opiopan/simhid-g1000/firmware/src/command.c

/*
 * command.c
 *  Author: Hiroshi Murayama <opiopan@gmail.com>
 */

#include <stdio.h>
#include <string.h>
#include <ctype.h>
#include "project.h"
#include "appmain.h"
#include "option.h"
#include "version.h"
#include "command.h"
#include "olog.h"

static const char* PRODUCTNAME = "SimHID G1000";
static const char* MANUFACTURER = "Hiroshi Murayama <opiopan@gmail.com>";
static const char* PROTOCOL = "SimHID protocol V1";

/*========================================================
 Error message
========================================================*/
static const char *ERR_SYNTAX = "syntax error";
static const char* ERR_TOOLONG = "too long line";
static const char* ERR_TOOMANYPARAM = "parameters of command must be less than 10";
static const char* ERR_NOCMD = "not supported command";
static const char* ERR_NOOPT = "unknown option name";
static const char *ERR_INVBOOLOPT = "option value must be 0 or 1";
static const char *ERR_INVINTOPT = "option value must be integer";
static const char *ERR_TOOLONGOPT = "too long option value";

/*========================================================
 Command parser implementation
========================================================*/
void command_parser_init(CommandParserCtx * ctx, char *buf, int len)
{
    ctx->phase = PARSE_INIT;
    ctx->linebuf = buf;
    ctx->linebuflen = len;
    ctx->parsedlen = 0;
    ctx->paramnum = 0;
    ctx->command = -1;
    ctx->err = NULL;
}

static inline BOOL isSeparator(int c)
{
    return c == ' ' || c == '\t';
}

static inline BOOL isCommand(int c)
{
    return (c >= 'A' && c <= 'Z') || (c >= 'a' && c <= 'z');
}

static inline BOOL isNumeric(int c)
{
    return c >= '0' && c <= '9';
}

BOOL command_parser_parse(CommandParserCtx *ctx, int c)
{
    BOOL rc = FALSE;

    if (ctx->phase == PARSE_END){
        ctx->phase = PARSE_INIT;
        ctx->parsedlen = 0;
        ctx->paramnum = 0;
        ctx->command = -1;
        ctx->err = NULL;
    }

    if (ctx->parsedlen == ctx->linebuflen && ctx->phase != PARSE_SKIP){
        ctx->phase = PARSE_SKIP;
        ctx->err = ERR_TOOLONG;
    }
    if (ctx->phase != PARSE_SKIP || ctx->phase != PARSE_EOL){
        ctx->linebuf[ctx->parsedlen++] = c;
    }

    switch (ctx->phase){
    case PARSE_INIT:{
        if (isSeparator(c)){
            /* nothing to do */
        }else if (isCommand(c)){
            ctx->phase = PARSE_POSTCOMMAND;
            ctx->command = c;
        }else if (c == '\r'){
            ctx->phase = PARSE_EOL;
        }else{
            ctx->phase = PARSE_SKIP;
            ctx->err = ERR_SYNTAX;
        }
        break;
    }
    case PARSE_POSTCOMMAND:{
        if (isSeparator(c)){
            ctx->phase = PARSE_SEPARATOR;
        }else if (c == '\r'){
            ctx->phase = PARSE_EOL;
        }else{
            ctx->phase = PARSE_SKIP;
            ctx->err = ERR_SYNTAX;
        }
        break;
    }
    case PARSE_SEPARATOR:{
        if (isSeparator(c)){
            /* nothing to do */
        }else if (c == '\r'){
            ctx->phase = PARSE_EOL;
        }else if (ctx->paramnum >= COMMAND_MAX_PARAM){
            ctx->phase = PARSE_SKIP;
            ctx->err = ERR_TOOMANYPARAM;
        }else{
            CommandParam* param = ctx->params + ctx->paramnum++;
            param->strvalue = ctx->linebuf + ctx->parsedlen - 1;
            param->isNumber = FALSE;
            param->len = 1;
            if (c == '-'){
                ctx->phase = PARSE_MINUSNUMBER;
            }else if (isNumeric(c)){
                ctx->phase = PARSE_NUMBER;
                param->numvalue = c - '0';
            }else{
                ctx->phase = PARSE_STRING;
            }
        }
        break;
    }
    case PARSE_MINUSNUMBER:{
        if (isSeparator(c)){
            ctx->phase = PARSE_SEPARATOR;
        }else if (c == '\r'){
            ctx->phase = PARSE_EOL;
        }else{
            CommandParam *param = ctx->params + ctx->paramnum - 1;
            param->len++;
            if (isNumeric(c)){
                ctx->phase = PARSE_NUMBER;
                param->numvalue = -(c - '0');
            }else{
                ctx->phase = PARSE_STRING;
            }
        }
        break;
    }
    case PARSE_NUMBER:{
        CommandParam *param = ctx->params + ctx->paramnum - 1;
        if (isSeparator(c)){
            ctx->phase = PARSE_SEPARATOR;
            param->isNumber = TRUE;
            ctx->linebuf[ctx->parsedlen - 1] = '\0';
        }else if (c == '\r'){
            ctx->phase = PARSE_EOL;
            param->isNumber = TRUE;
            ctx->linebuf[ctx->parsedlen - 1] = '\0';
        }else{
            param->len++;
            if (isNumeric(c)){
                param->numvalue *= 10;
                param->numvalue += param->numvalue > 0 ? 
                                   c - '0' : -(c - '0');
            }else{
                ctx->phase = PARSE_STRING;
            }
        }
        break;
    }
    case PARSE_STRING:{
        CommandParam *param = ctx->params + ctx->paramnum - 1;
        if (isSeparator(c)){
            ctx->phase = PARSE_SEPARATOR;
            ctx->linebuf[ctx->parsedlen - 1] = '\0';
        }else if (c == '\r'){
            ctx->linebuf[ctx->parsedlen - 1] = '\0';
            ctx->phase = PARSE_EOL;
        }else{
            param->len++;
        }
        break;
    }
    case PARSE_SKIP:{
        if (c == '\r'){
            ctx->phase = PARSE_EOL;
        }
        break;
    }
    case PARSE_EOL:{
        if (c == '\n'){
            ctx->phase = PARSE_END;
            rc = TRUE;
        }else{
            ctx->phase = PARSE_SKIP;
            ctx->err = ERR_SYNTAX;
        }
        break;
    }
    case PARSE_END:{
        /* no condition reach here */
        break;
    }
    }

    return rc;
}

/*========================================================
 Individual command implementation
========================================================*/

/*--------------------------------------------------------
 NOP command
--------------------------------------------------------*/
static void nop_init(void *ctx, CommandParserCtx *cmd)
{
}

static int nop_schedule(void *ctx, char *respbuf, int len)
{
    return 0;
}

static BOOL nop_isfinished(void *ctx)
{
    return TRUE;
}

static CMDOPS cmd_nop = {
    .init = nop_init,
    .schedule = nop_schedule,
    .isfinished = nop_isfinished,
};

/*--------------------------------------------------------
 Error response command
--------------------------------------------------------*/
typedef struct{
    const char* msg;
}ERRCTX;

static void err_init(void *ctx, CommandParserCtx *cmd)
{
    ERRCTX* rctx = (ERRCTX*)ctx;
    rctx->msg = cmd->err;
}

static int err_schedule(void *ctx, char *respbuf, int len)
{
    ERRCTX *rctx = (ERRCTX *)ctx;
    return snprintf(respbuf, len, "E %s\r\n", rctx->msg);
}

static BOOL err_isfinished(void *ctx)
{
    return TRUE;
}

static CMDOPS cmd_err = {
    .init = err_init,
    .schedule = err_schedule,
    .isfinished = err_isfinished,
};

/*--------------------------------------------------------
 Identifier command
--------------------------------------------------------*/
typedef struct{
    int line;
    int maxline;
    int swg_num;
}IDCTX;

static void id_init(void *ctx, CommandParserCtx *cmd)
{
    IDCTX* rctx = (IDCTX*)ctx;
    SCANNER_CTX *scanner = app_getScannerCtx();
    rctx->swg_num = scanner_getswgnum(scanner);
    if (cmd->paramnum > 0 && (strcmp(cmd->params[0].strvalue, "b") == 0 || strcmp(cmd->params[0].strvalue, "B") == 0)){
        rctx->line = 4;
        rctx->maxline = 6 + rctx->swg_num;
    }else{
        rctx->line = 0;
#ifdef ENABLE_RICH_IDENTIFIER
        rctx->maxline == 6 + rctx->swg_num;
#else
        rctx->maxline = 4;
#endif
    }
}

static int id_schedule(void *ctx, char *respbuf, int len)
{
    IDCTX *rctx = (IDCTX *)ctx;
    rctx->line++;
    if (rctx->line == 1){
        return snprintf(respbuf, len, "I Product Name: %s\r\n", PRODUCTNAME);
    }else if (rctx->line == 2){
        return snprintf(respbuf, len, "I Manufacturer: %s\r\n", MANUFACTURER);
    }else if (rctx->line == 3){
        return snprintf(respbuf, len, "I Firmware Version: %s\r\n", version_string);
    }else if (rctx->line == 4){
        return snprintf(respbuf, len, "I Protocol: %s\r\n", PROTOCOL);
    }else if (rctx->line == 5){
        return snprintf(respbuf, len, "I BIT Result:");
    }else if (rctx->line < 6 + rctx->swg_num){
        SCANNER_CTX *scanner = app_getScannerCtx();
        VSWG_CTX* swg =  scanner_getswg(scanner, rctx->line - 6);
        const char* status = swg->is_valid ? "OK" : "Failure";
        return snprintf(respbuf, len, " [%s = %s]", swg->name, status);
    }else if (rctx->line == 6 + rctx->swg_num){
        return snprintf(respbuf, len, "\r\n");
    }

    return 0;
}

static BOOL id_isfinished(void *ctx)
{
    IDCTX *rctx = (IDCTX *)ctx;
    return rctx->line >= rctx->maxline;
}

static CMDOPS cmd_id = {
    .init = id_init,
    .schedule = id_schedule,
    .isfinished = id_isfinished,
};

/*--------------------------------------------------------
 Retrieving switch definitions command
--------------------------------------------------------*/
typedef struct {
    int swgix;
    int swix;
    BOOL completed;
}SWDEFCTX;

static void swdef_init(void *ctx, CommandParserCtx *cmd)
{
    SWDEFCTX* rctx = (SWDEFCTX*)ctx;
    *rctx = (SWDEFCTX){};
}

static int swdef_schedule(void *ctx, char *respbuf, int len)
{
    SWDEFCTX* rctx = (SWDEFCTX*)ctx;
    if (rctx->swgix < 0){
        rctx->completed = TRUE;
        return strlcpy(respbuf, "D\r\n", len);
    }

    SCANNER_CTX *scanner = app_getScannerCtx();
    VSWG_CTX* swg = scanner_getswg(scanner, rctx->swgix);
    VSWITCH_CTX* sw = SWG_GET_SWITCH(swg, rctx->swix);

    int rc = snprintf(respbuf, len, "D %s ", sw->name);
    rc += sw->ops->printdef(sw, respbuf + rc, len - rc);
    rc += strlcpy(respbuf + rc, "\r\n", len - rc);

    rctx->swix++;
    if (rctx->swix >= SWG_GET_SWITCHNUM(swg)){
        rctx->swgix++;
        rctx->swix = 0;
        if (rctx->swgix > scanner_getswgnum(scanner)){
            rctx->swgix = -1;
            rctx->swix = -1;
        }
    }

    return rc;
}

static BOOL swdef_isfinished(void *ctx)
{
    SWDEFCTX *rctx = (SWDEFCTX *)ctx;
    return rctx->completed;
}

static CMDOPS cmd_swdef = {
    .init = swdef_init,
    .schedule = swdef_schedule,
    .isfinished = swdef_isfinished,
};

/*--------------------------------------------------------
 Retrieving or Setting option value command
--------------------------------------------------------*/
typedef struct {
    int index;
    BOOL isCountinuous;
    const char* err;
}OPTCTX;

static void opt_init(void *ctx, CommandParserCtx *cmd)
{
    OPTCTX* rctx = (OPTCTX*)ctx;
    rctx->err = NULL;
    if (cmd->paramnum == 0){
        rctx->index = 0;
        rctx->isCountinuous = TRUE;
    }else{
        rctx->isCountinuous = FALSE;
        const char* name = cmd->params[0].strvalue;
        for (char* pt = (char*)name; *pt; pt++){
            *pt = toupper(*pt);
        }
        OPTION_DEF* def = NULL;
        rctx->index = -1;
        for (int i = 0; i < option_getOptNum(); i++){
            def = option_getOptDef(i);
            if (strcmp(def->name, name) == 0){
                rctx->index = i;
                break;
            }
        }
        if (rctx->index < 0){
            rctx->err = ERR_NOOPT;
            return;
        }
        if (cmd->paramnum >= 2){
            CommandParam* value = cmd->params + 1;
            OPTION_VALUE newval;
            if (def->type == OPTVAL_BOOL){
                if (!value->isNumber || value->numvalue < 0 || value->numvalue > 1){
                    rctx->err = ERR_INVBOOLOPT;
                    return;
                }
                newval.data.boolval = value->numvalue;
            }else if (def->type == OPTVAL_INTEGER){
                if (!value->isNumber){
                    rctx->err = ERR_INVINTOPT;
                    return;
                }
                newval.data.intval = value->numvalue;
            }else if (def->type == OPTVAL_STRING){
                if (value->len >= def->maxlen){
                    rctx->err = ERR_TOOLONGOPT;
                    return;
                }
                newval.data.strval = value->strvalue;
            }
            newval.type = def->type;
            option_setValue(rctx->index, newval);
        }
    }
}

static int opt_schedule(void *ctx, char *respbuf, int len)
{
    OPTCTX* rctx = (OPTCTX*)ctx;
    int rc;
    if (rctx->err){
        rctx->isCountinuous = FALSE;
        rc = snprintf(respbuf, len, "E %s\r\n", rctx->err);
    }else{
        OPTION_DEF* def = option_getOptDef(rctx->index);
        OPTION_VALUE val = option_getValue(rctx->index);
        if (val.type == OPTVAL_STRING){
            rc = snprintf(respbuf, len, "O %s %s\r\n", def->name, val.data.strval);
        }else{
            rc = snprintf(respbuf, len, "O %s %d\r\n", def->name, val.data.intval);
        }
        rctx->index++;
        if (rctx->index >= option_getOptNum()){
            rctx->isCountinuous = FALSE;
        }

    }
    return rc;
}

static BOOL opt_isfinished(void *ctx)
{
    OPTCTX* rctx = (OPTCTX*)ctx;
    return !rctx->isCountinuous;
}

static CMDOPS cmd_opt = {
    .init = opt_init,
    .schedule = opt_schedule,
    .isfinished = opt_isfinished,
};

/*========================================================
 Command executor implementation
========================================================*/
void command_executor_init(CommandExecutorCtx *ctx, CommandParserCtx *command)
{
    ctx->status = CMD_INIT;
    int cmdchr = command->command;
    if (command->err){
        OLOG_LOGD("commmand: parsing error");
        ctx->ops = &cmd_err;
    }else if (cmdchr < 0){
        OLOG_LOGD("commmand: NOP");
        ctx->ops = &cmd_nop;
    }else if (cmdchr == 'i' || cmdchr == 'I'){
        OLOG_LOGD("command: INFORMAITON command");
        ctx->ops = &cmd_id;
    }else if (cmdchr == 'd' || cmdchr == 'D'){
        OLOG_LOGD("command: DEFINITION command");
        ctx->ops = &cmd_swdef;
    }else if (cmdchr == 'o' || cmdchr == 'O'){
        OLOG_LOGD("command: OPTION command");
        ctx->ops = &cmd_opt;
    }else{
        OLOG_LOGD("command: unsupported command [%c]", cmdchr);
        command->err = ERR_NOCMD;
        ctx->ops = &cmd_err;
    }
    ctx->ops->init(ctx->cmdcontext, command);
}

int command_exectutor_schedule(CommandExecutorCtx *ctx, char *respbuf, int len)
{
    int rc = 0;
    if (ctx->status != CMD_COMPLETE){
        rc = ctx->ops->schedule(ctx->cmdcontext, respbuf, len);
        if (ctx->ops->isfinished(ctx->cmdcontext)){
            ctx->status = CMD_COMPLETE;
        }else{
            ctx->status = CMD_EXECUTING;
        }
    }
    return rc;
}
