opiopan/simhid-g1000/firmware/src/hrtimer.h

/*
 * hrtimer.h
 *  Author: opiopan@gmail.com
 */
#ifndef HRTIMER_H_
#define HRTIMER_H_

#include "project.h"

#define HRTIMER_MILISEC 1000
#define HRTIMER_SEC (1000 * 1000)

extern TIM_HandleTypeDef* hrtimer_handler;

#define HRTIMER_GETTIME() ((int32_t)__HAL_TIM_GET_COUNTER(hrtimer_handler))

void hrtimer_init(TIM_HandleTypeDef* handler);

#endif
